Tracy-115/NewBruinsOnTheBlock/NBOTB Website/src/assets/jump-cover.png

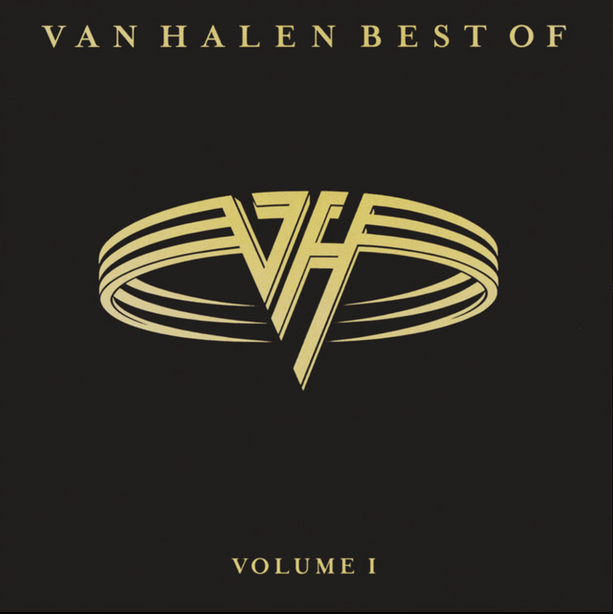
NBOTB Website/src/assets/jump-cover.png
