Tracy-115/NewBruinsOnTheBlock/NBOTB Website/src/assets/NBOTB_Christian.PNG

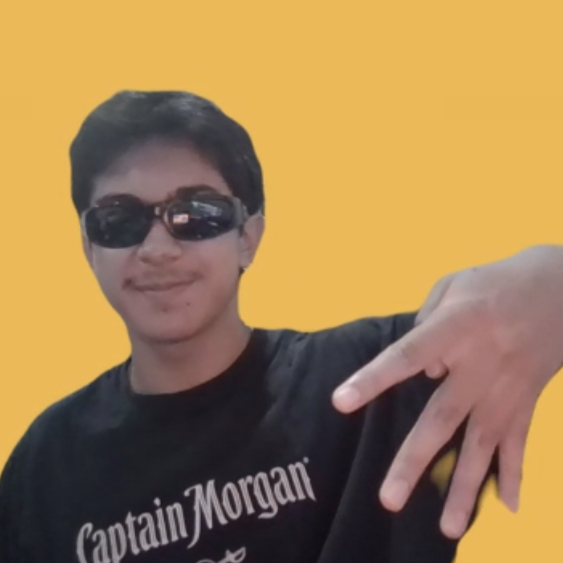
NBOTB Website/src/assets/NBOTB_Christian.PNG
