Tracy-115/NewBruinsOnTheBlock/NBOTB Website/src/assets/NBOTB_Suhana.PNG

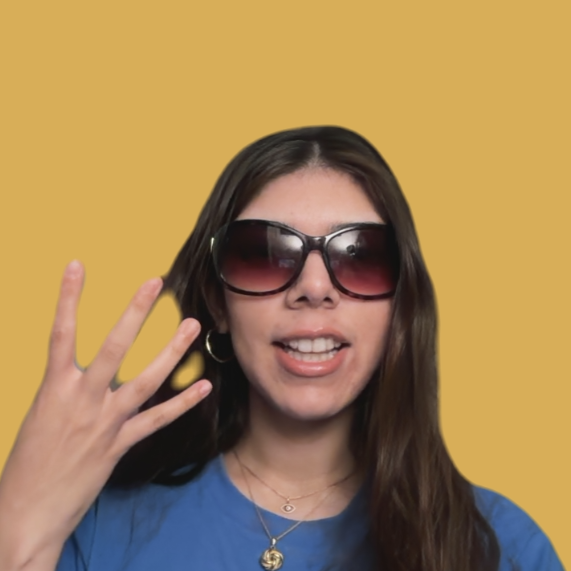
NBOTB Website/src/assets/NBOTB_Suhana.PNG
