Tracy-115/NewBruinsOnTheBlock/NBOTB Website/src/assets/NewBruinsOnTheBlock_photo.png

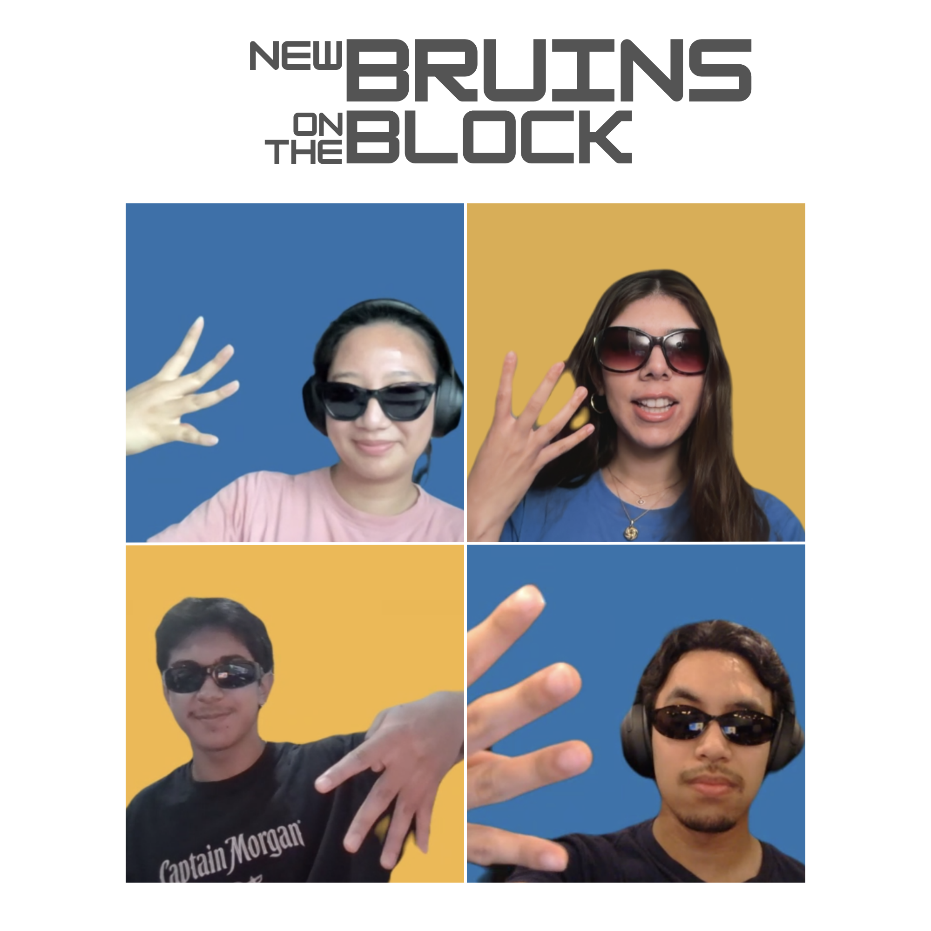
NBOTB Website/src/assets/NewBruinsOnTheBlock_photo.png
